rrainey/tempo/hardware/tempo-bt/models/S2B-PH-SM4-TB(LF)(SN)--3DModel-STEP-56544.STEP

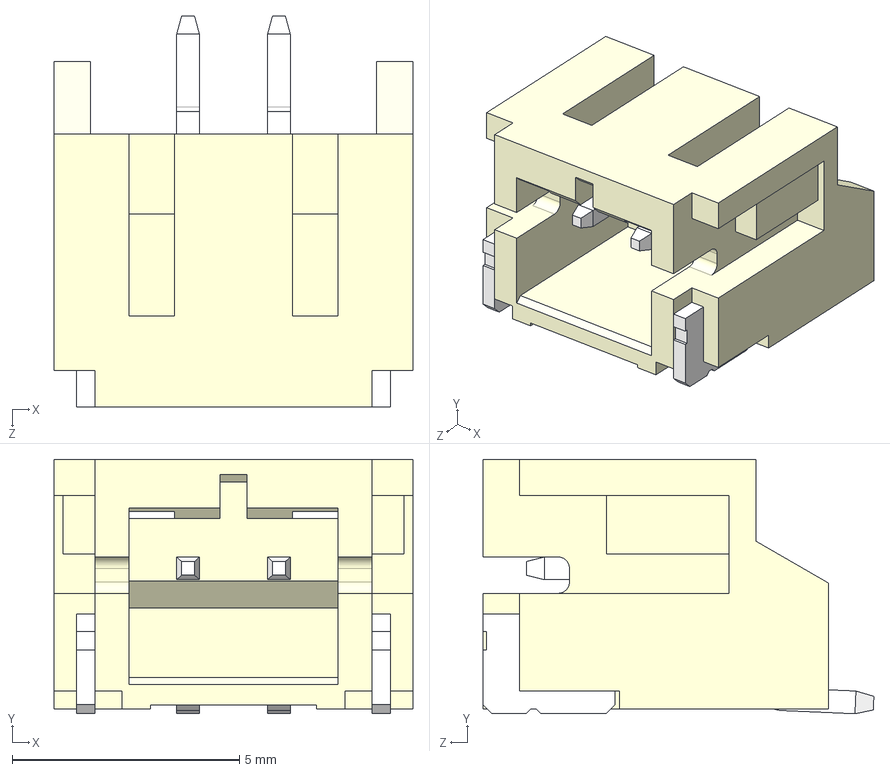
[picture p21: CAD file, 2023-10-15]
hardware/tempo-bt/models/S2B-PH-SM4-TB(LF)(SN)--3DModel-STEP-56544.STEP
7.90 x 5.60 x 8.60 mm
