rrainey/tempo/hardware/tempo-bt/models/QFN24_4X4X0P9_IVS.step

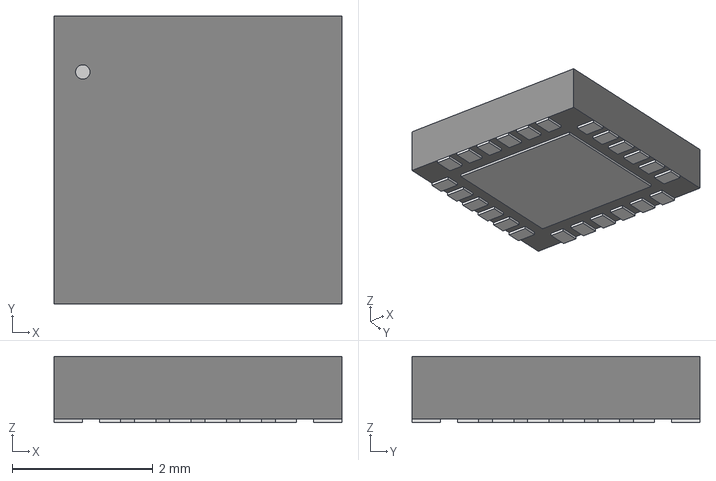
[picture p22: CAD file, 2023-10-15]
hardware/tempo-bt/models/QFN24_4X4X0P9_IVS.step
4.09 x 4.09 x 0.942 mm
