rrainey/tempo/hardware/tempo-bt/models/ICM-42688-P.step

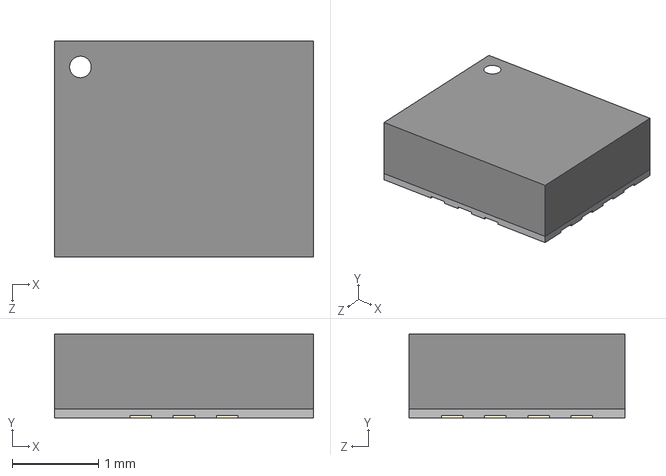
[picture p23: CAD file, 2023-10-15]
hardware/tempo-bt/models/ICM-42688-P.step
3.00 x 0.97 x 2.50 mm
