rrainey/tempo/hardware/tempo-bt/models/MEM2061-01-188-00-A.stp

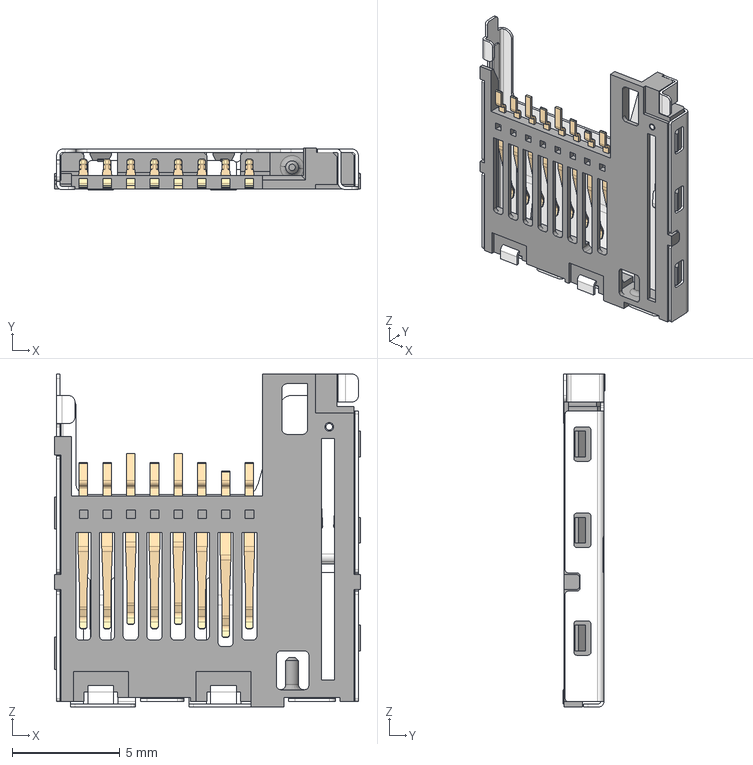
[picture p24: CAD file, 2023-10-15]
hardware/tempo-bt/models/MEM2061-01-188-00-A.stp
14.2 x 1.95 x 15.5 mm
ÇÐ³ý-ÀÉì2[2]
ÇÐ³ý-ÀÉì-±¡±Ú2
