rrainey/tempo/hardware/tempo-bt/models/PCB-outline.dxf

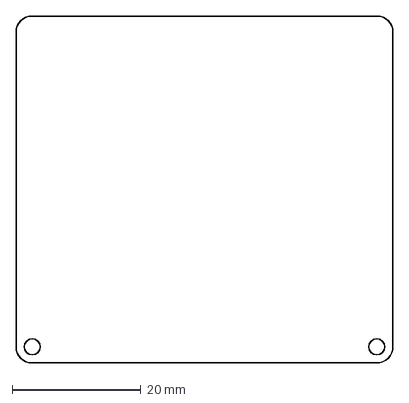
[picture p25: CAD file, 2023-10-15]
hardware/tempo-bt/models/PCB-outline.dxf
58.4 x 53.8 mm
