rrainey/tempo/hardware/tempo-bt/models/7945-1-15-20-09-14-11-0.stp

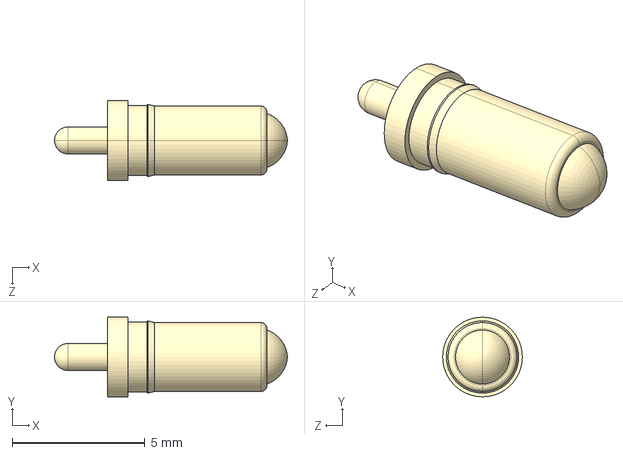
[picture p26: CAD file, 2023-10-15]
hardware/tempo-bt/models/7945-1-15-20-09-14-11-0.stp
8.76 x 3.00 x 3.00 mm
