rrainey/tempo/hardware/tempo-bt/models/TQFP48_7x7MC_MCH.step

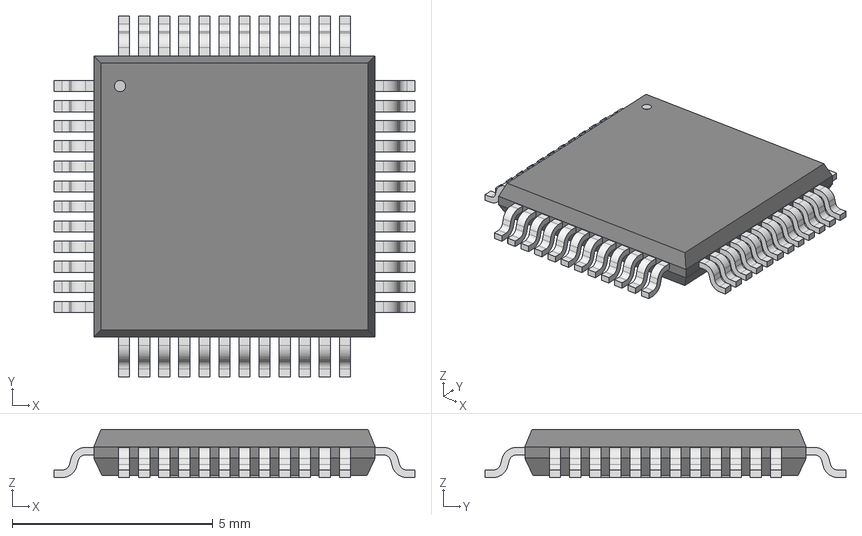
[picture p27: CAD file, 2023-10-15]
hardware/tempo-bt/models/TQFP48_7x7MC_MCH.step
8.99 x 8.99 x 1.20 mm
