rrainey/tempo/hardware/tempo-bt/models/DPS310XTSA1.stp

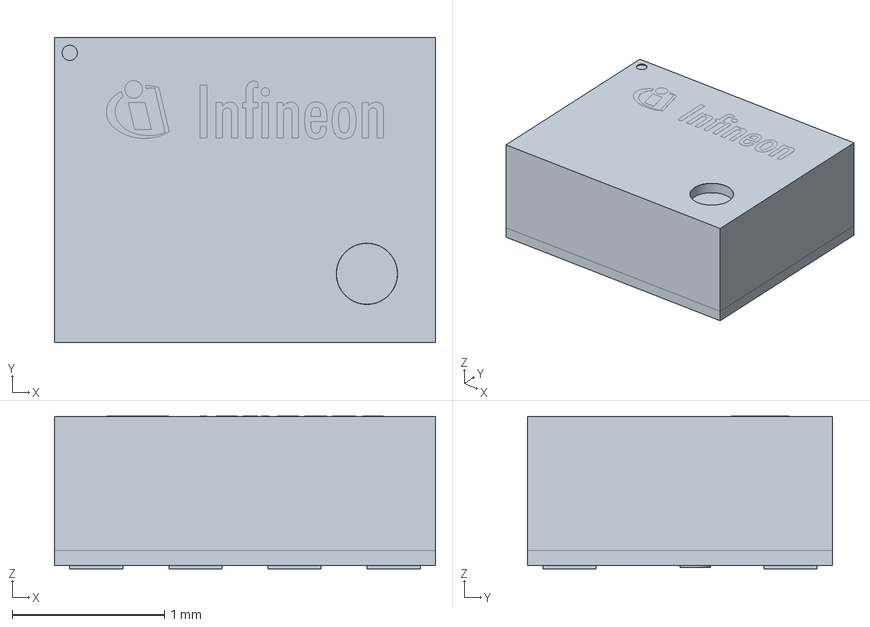
[picture p28: CAD file, 2023-10-15]
hardware/tempo-bt/models/DPS310XTSA1.stp
2.50 x 2.00 x 1.00 mm
CADSOFTTOOLS 2.1
CADSOFTTOOLS 2.2
CADSOFTTOOLS 2.3
CADSOFTTOOLS 2.4
CADSOFTTOOLS 2.5
CADSOFTTOOLS 2.6
CADSOFTTOOLS 2.7
CADSOFTTOOLS 2.8
CADSOFTTOOLS 2.9
CADSOFTTOOLS 2.10
CADSOFTTOOLS 2.11
CADSOFTTOOLS 2.12
CADSOFTTOOLS 2.13
CADSOFTTOOLS 2.14
CADSOFTTOOLS 2.15
CADSOFTTOOLS 2.16
CADSOFTTOOLS 2.17
CADSOFTTOOLS 2.18
CADSOFTTOOLS 2.19
CADSOFTTOOLS 2.20
CADSOFTTOOLS 2.21
CADSOFTTOOLS 2.22
CADSOFTTOOLS 2.23
CADSOFTTOOLS 2.24
CADSOFTTOOLS 2.25
CADSOFTTOOLS 2.26
CADSOFTTOOLS 2.27
CADSOFTTOOLS 2.28
CADSOFTTOOLS 2.29
CADSOFTTOOLS 2.30
CADSOFTTOOLS 2.31
CADSOFTTOOLS 2.32
CADSOFTTOOLS 2.33
CADSOFTTOOLS 2.34
CADSOFTTOOLS 2.35
CADSOFTTOOLS 2.36
CADSOFTTOOLS 2.37
CADSOFTTOOLS 2.38
CADSOFTTOOLS 2.39
CADSOFTTOOLS 2.40
CADSOFTTOOLS 2.41
CADSOFTTOOLS 2.42
CADSOFTTOOLS 2.43
CADSOFTTOOLS 2.44
CADSOFTTOOLS 2.45
CADSOFTTOOLS 2.46
CADSOFTTOOLS 2.47
CADSOFTTOOLS 2.48
CADSOFTTOOLS 2.49
CADSOFTTOOLS 2.50
CADSOFTTOOLS 2.51
CADSOFTTOOLS 2.52
CADSOFTTOOLS 2.53
CADSOFTTOOLS 2.54
CADSOFTTOOLS 2.55
CADSOFTTOOLS 2.56
CADSOFTTOOLS 2.57
CADSOFTTOOLS 2.58
CADSOFTTOOLS 2.59
CADSOFTTOOLS 2.60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
