rrainey/tempo/hardware/tempo-bt/models/LGA10_BMP390_BOS.step

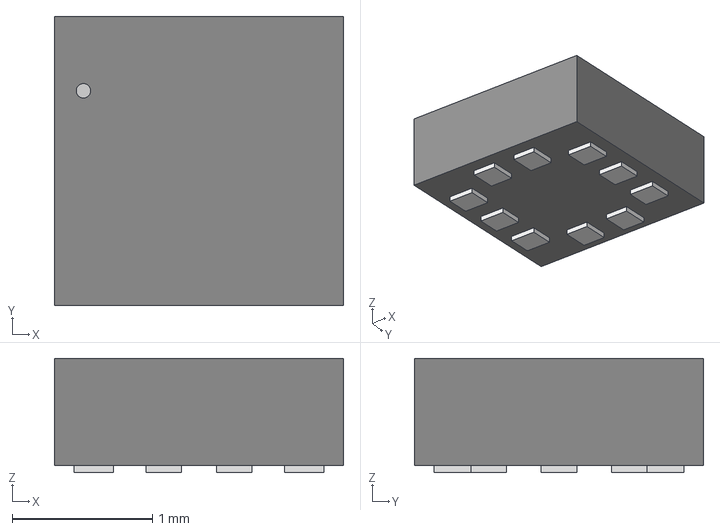
[picture p29: CAD file, 2023-10-15]
hardware/tempo-bt/models/LGA10_BMP390_BOS.step
2.06 x 2.06 x 0.815 mm
