rrainey/tempo/zephyr/tempo-bt-v1/include/app_init.h

/*
 * SPDX-License-Identifier: Apache-2.0
 * 
 * Tempo-BT V1 - Application Initialization Header
 */

#ifndef APP_INIT_H
#define APP_INIT_H

int app_init(void);

/**
 * @brief Initialize the storage subsystem
 * 
 * Mounts LittleFS and creates necessary directories
 * 
 * @return 0 on success, negative error code on failure
 */
int app_storage_init(void);

#endif /* APP_INIT_H */
